usgdev/CoVen19/CoVen19_v0.7/DXF/side_enclosure_left.DXF

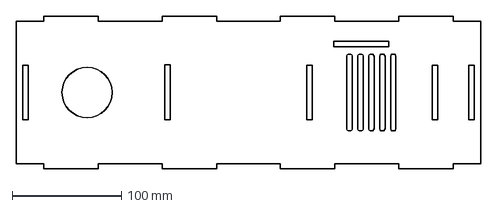
[picture p24: CAD file, 2020-04-14]
CoVen19_v0.7/DXF/side_enclosure_left.DXF
425.0 x 140.0 mm
