usgdev/CoVen19/CoVen19_v0.7/STL/arduino_Uno_r3-1.STL

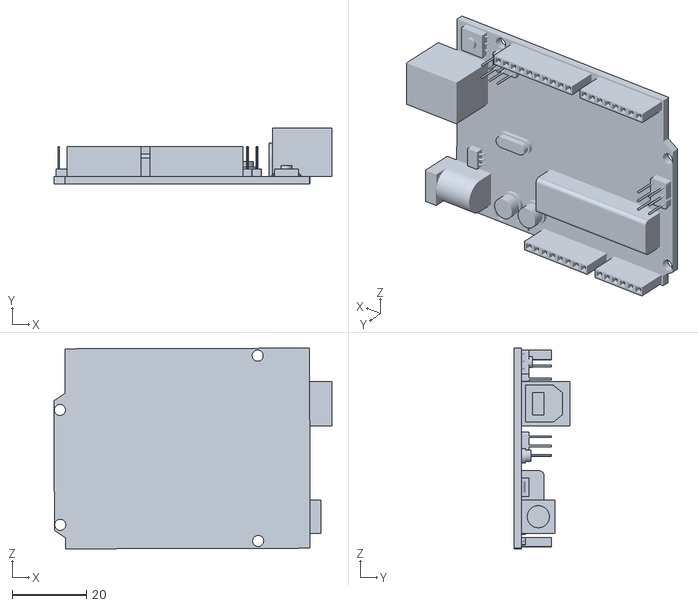
[picture p25: CAD file, 2020-04-14]
CoVen19_v0.7/STL/arduino_Uno_r3-1.STL
75.0 x 15.0 x 54.2
