usgdev/CoVen19/CoVen19_v0.7/DXF/nema_mount_plate.DXF

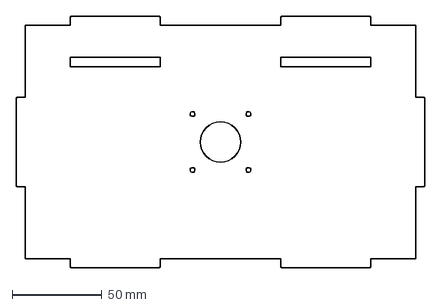
[picture p26: CAD file, 2020-04-14]
CoVen19_v0.7/DXF/nema_mount_plate.DXF
227.0 x 140.0 mm
