usgdev/CoVen19/CoVen19_v0.7/STL/actuator_arm_left-1.STL

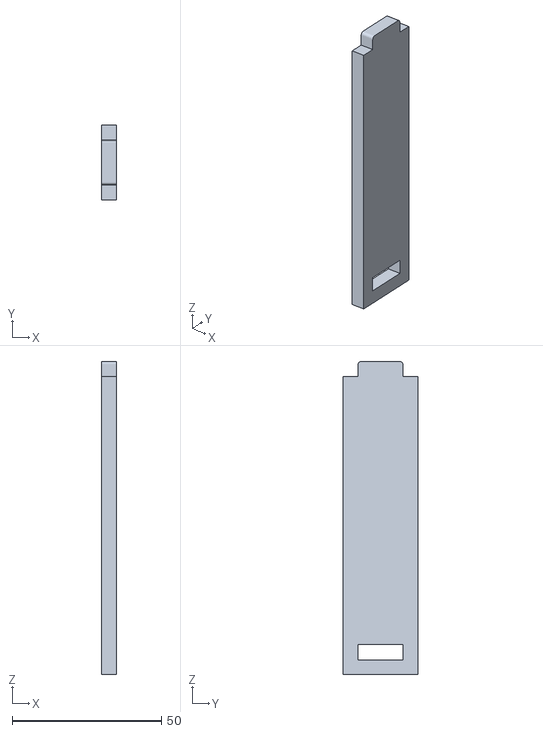
[picture p27: CAD file, 2020-04-14]
CoVen19_v0.7/STL/actuator_arm_left-1.STL
5.00 x 25.0 x 105.0
