usgdev/CoVen19/CoVen19_v0.7/STL/nema_17_motor-1.STL

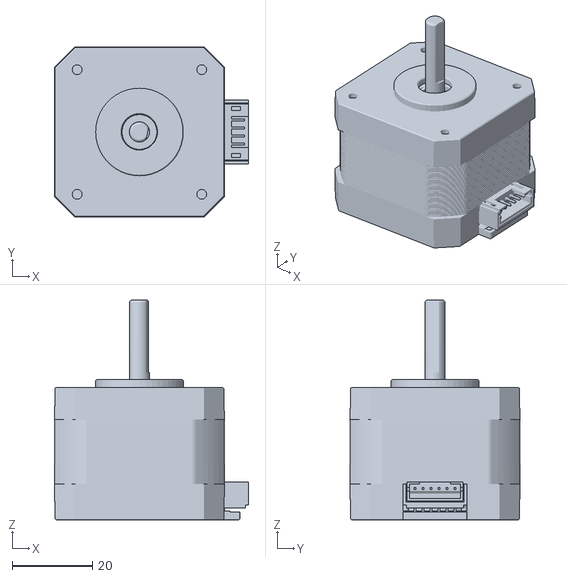
[picture p28: CAD file, 2020-04-14]
CoVen19_v0.7/STL/nema_17_motor-1.STL
48.3 x 42.3 x 54.8
