usgdev/CoVen19/CoVen19_v0.7/DXF/body_enclosure_cover.DXF

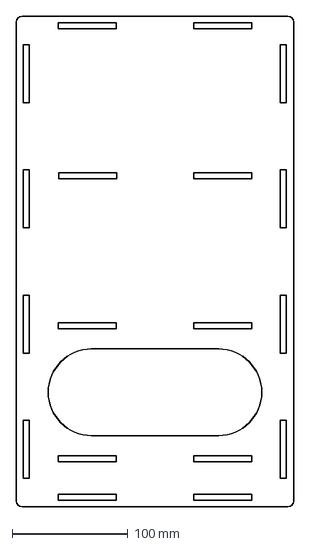
[picture p29: CAD file, 2020-04-14]
CoVen19_v0.7/DXF/body_enclosure_cover.DXF
240.0 x 425.0 mm
