usgdev/CoVen19/CoVen19_v0.7/STL/side_enclosure_left-1.STL

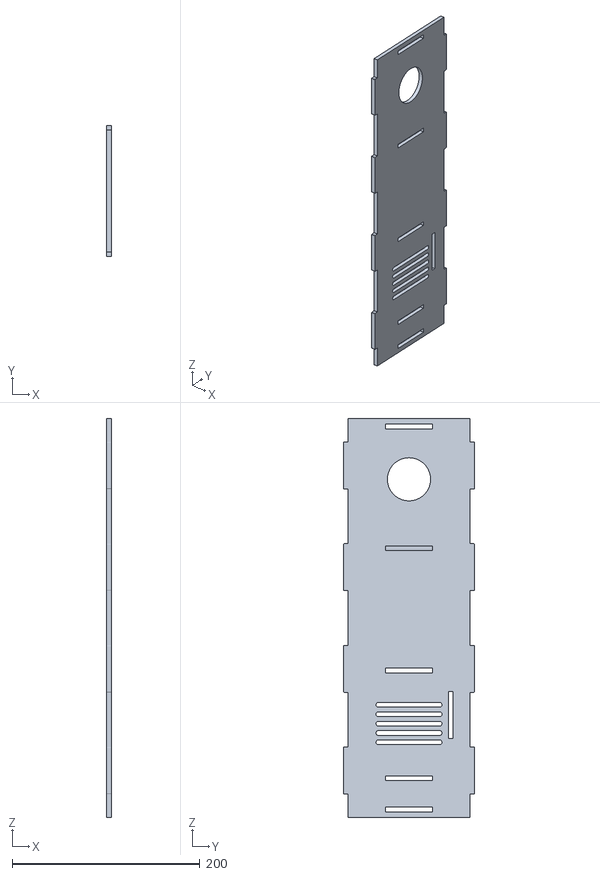
[picture p30: CAD file, 2020-04-14]
CoVen19_v0.7/STL/side_enclosure_left-1.STL
5.00 x 140.0 x 425.0
