usgdev/CoVen19/CoVen19_v0.7/DXF/pressure_plate_sloted.DXF

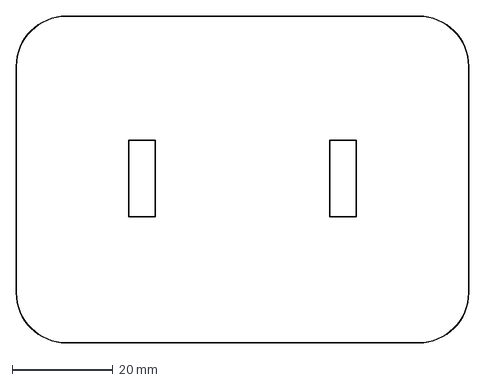
[picture p32: CAD file, 2020-04-14]
CoVen19_v0.7/DXF/pressure_plate_sloted.DXF
90.0 x 65.0 mm
