usgdev/CoVen19/CoVen19_v0.7/STL/pressure_plate_sloted-1.STL

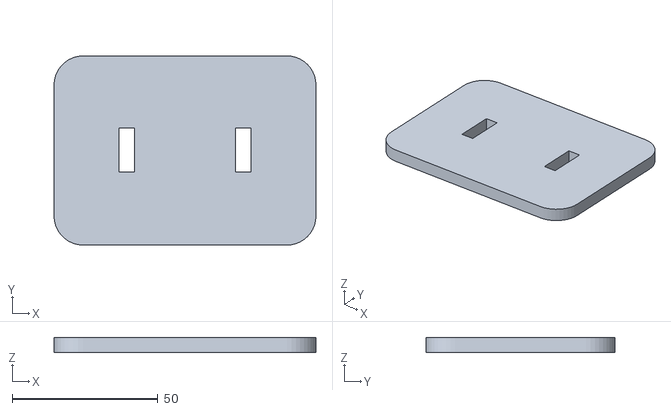
[picture p33: CAD file, 2020-04-14]
CoVen19_v0.7/STL/pressure_plate_sloted-1.STL
90.0 x 65.0 x 5.00
