usgdev/CoVen19/CoVen19_v0.7/STL/ambubag_air_release_plate-1.STL

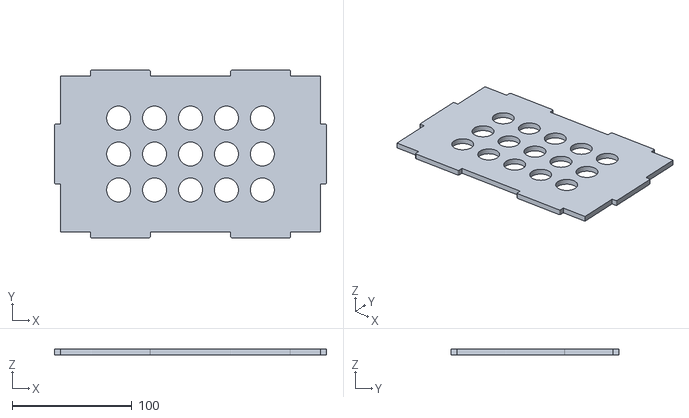
[picture p34: CAD file, 2020-04-14]
CoVen19_v0.7/STL/ambubag_air_release_plate-1.STL
227.0 x 140.0 x 5.00
