usgdev/CoVen19/CoVen19_v0.7/STL/ambu_bag-1.STL

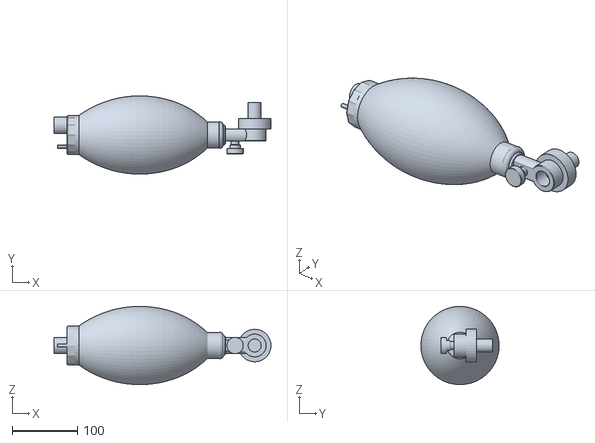
[picture p35: CAD file, 2020-04-14]
CoVen19_v0.7/STL/ambu_bag-1.STL
332.5 x 119.8 x 119.8
