usgdev/CoVen19/CoVen19_v0.7/STL/OLED_128x64-1.STL

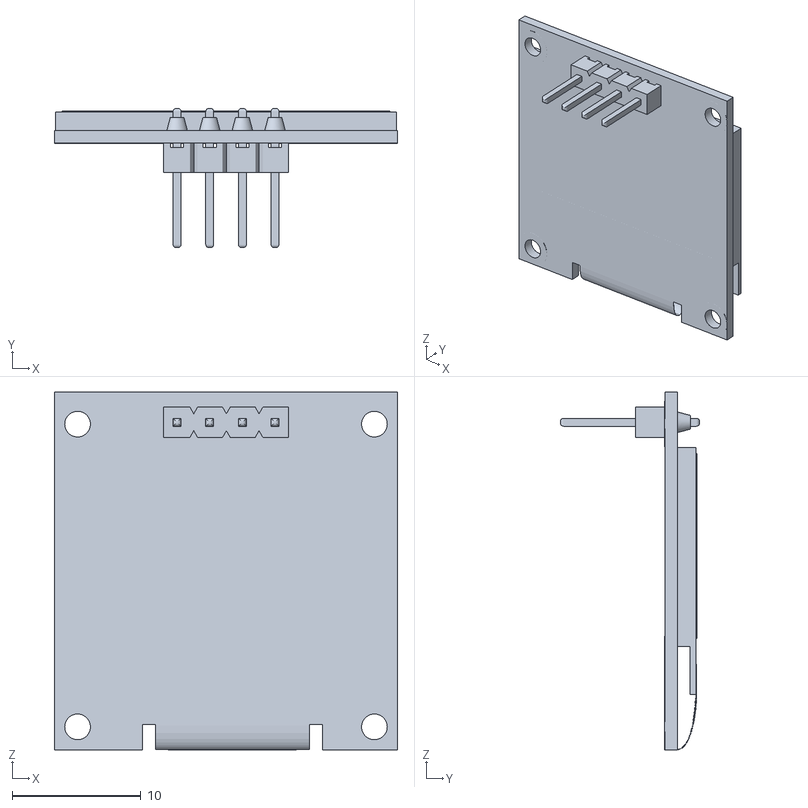
[picture p36: CAD file, 2020-04-14]
CoVen19_v0.7/STL/OLED_128x64-1.STL
26.7 x 10.8 x 27.9
