usgdev/CoVen19/CoVen19_v0.7/STL/body_handle_plate-1.STL

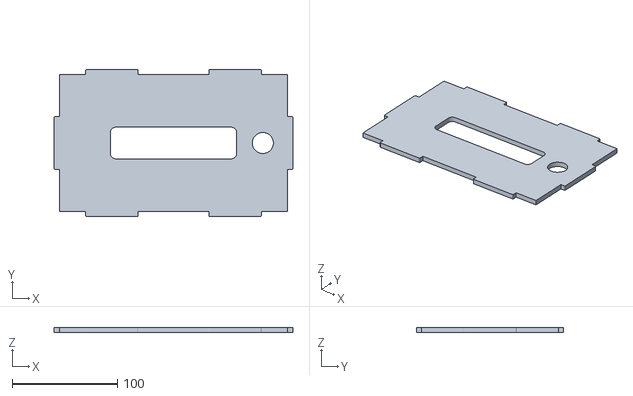
[picture p37: CAD file, 2020-04-14]
CoVen19_v0.7/STL/body_handle_plate-1.STL
227.0 x 140.0 x 5.00
