usgdev/CoVen19/CoVen19_v0.7/STL/electronics_mount_panel-1.STL

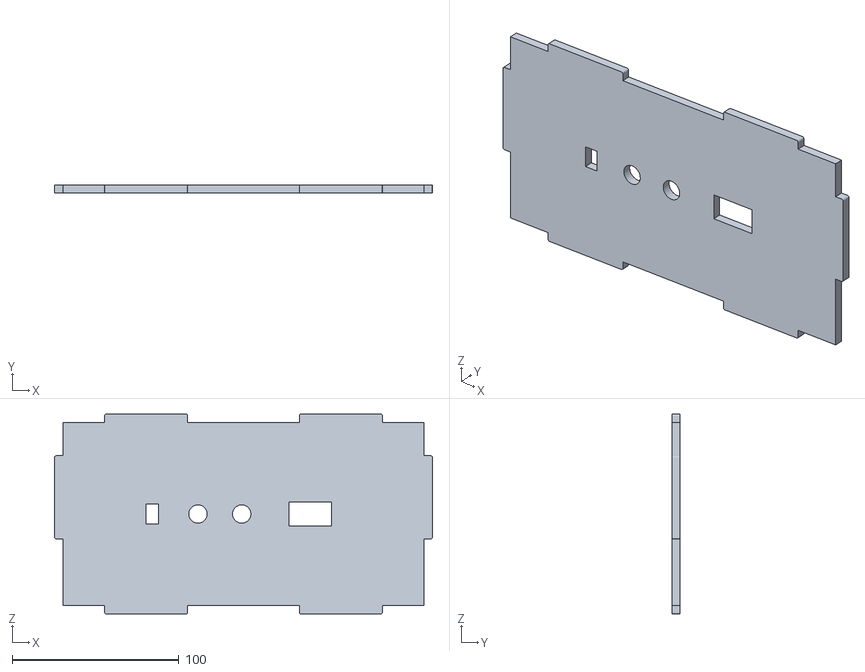
[picture p38: CAD file, 2020-04-14]
CoVen19_v0.7/STL/electronics_mount_panel-1.STL
227.0 x 5.00 x 120.0
