usgdev/CoVen19/CoVen19_v0.7/STL/body_base_plate-1.STL

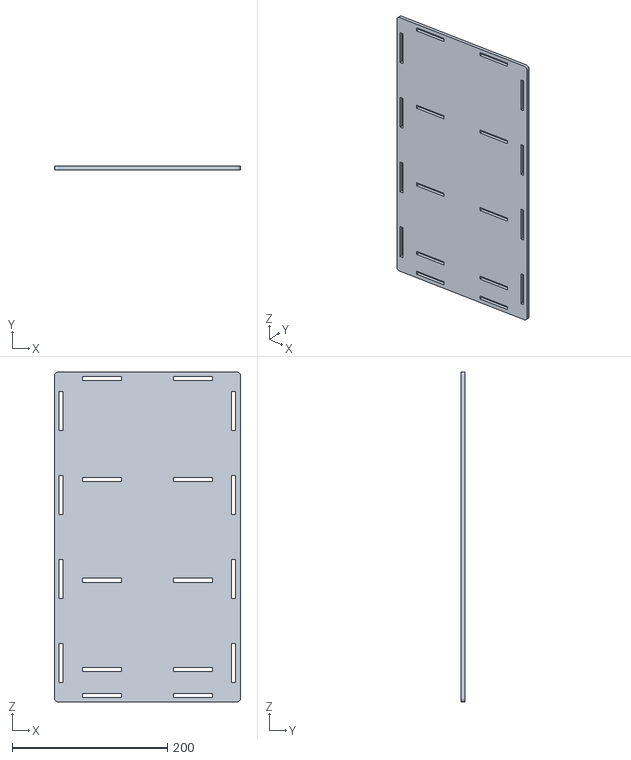
[picture p39: CAD file, 2020-04-14]
CoVen19_v0.7/STL/body_base_plate-1.STL
240.0 x 5.00 x 425.0
